salkinium/checkirona/pcb/stm32f4_adapter.sch

## EAGLE design pcb/stm32f4_adapter.sch (2015-05-14)

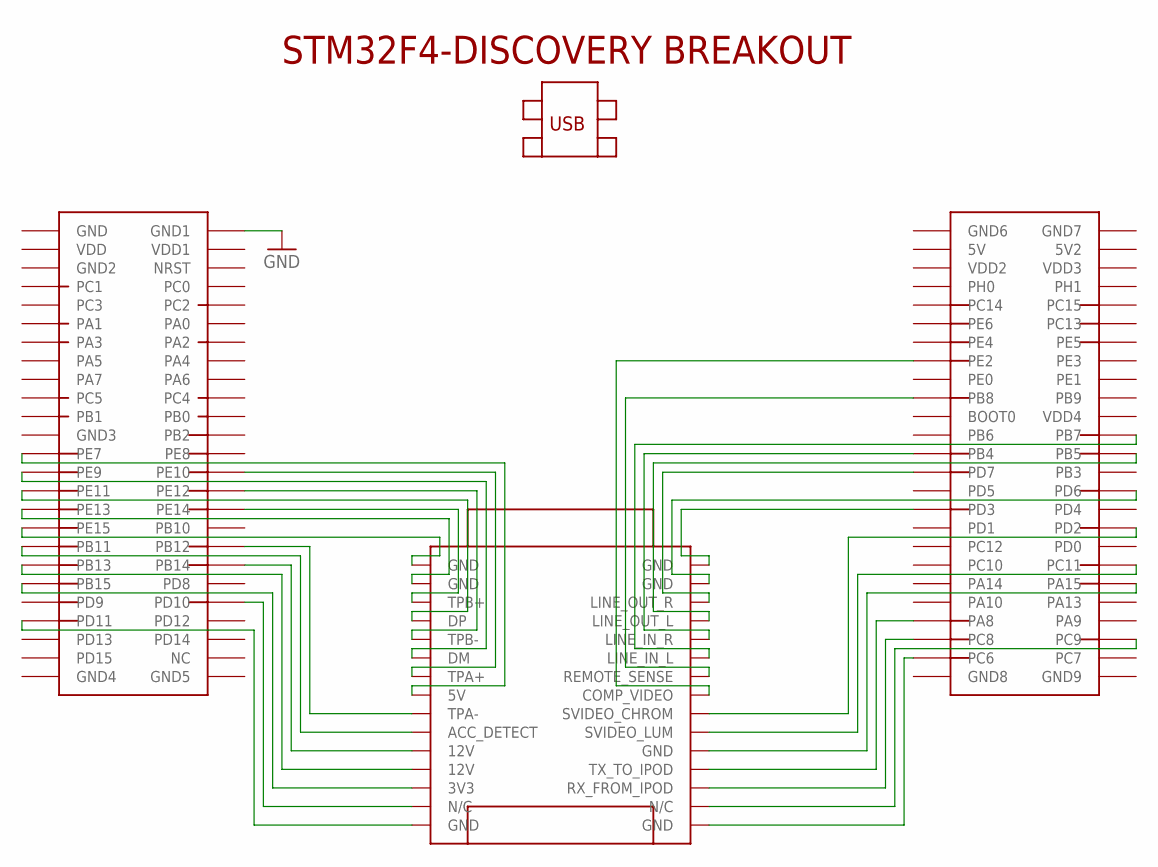
[picture p3: schematic stm32f4_adapter.sch]

Parts:
U$1: STM32F4-DISCOVERY
U$2: IPOD-CONNECTOR

Connections:
GND: U$1.P$2 (GND1)
unnamed: U$1.P$43 (PD11), U$2.P$16 (GND)
unnamed: U$1.P$42 (PD10), U$2.P$17 (N/C)
unnamed: U$1.P$39 (PB15), U$2.P$18 (3V3)
unnamed: U$1.P$38 (PB14), U$2.P$20 (12V)
unnamed: U$1.P$37 (PB13), U$2.P$19 (12V)
unnamed: U$1.P$36 (PB12), U$2.P$22 (TPA-)
unnamed: U$1.P$35 (PB11), U$2.P$21 (ACC_DETECT)
unnamed: U$1.P$33 (PE15), U$2.P$30 (GND)
unnamed: U$1.P$32 (PE14), U$2.P$28 (TPB+)
unnamed: U$1.P$31 (PE13), U$2.P$29 (GND)
unnamed: U$1.P$30 (PE12), U$2.P$26 (TPB-)
unnamed: U$1.P$29 (PE11), U$2.P$27 (DP)
unnamed: U$1.P$27 (PE9), U$2.P$25 (DM)
unnamed: U$1.P$28 (PE10), U$2.P$24 (TPA+)
unnamed: U$1.P$25 (PE7), U$2.P$23 (5V)
unnamed: U$1.P$97 (PC6), U$2.P$15 (GND)
unnamed: U$1.P$96 (PC9), U$2.P$14 (N/C)
unnamed: U$1.P$95 (PC8), U$2.P$13 (RX_FROM_IPOD)
unnamed: U$1.P$93 (PA8), U$2.P$12 (TX_TO_IPOD)
unnamed: U$1.P$90 (PA15), U$2.P$11 (GND)
unnamed: U$1.P$88 (PC11), U$2.P$10 (SVIDEO_LUM)
unnamed: U$1.P$84 (PD2), U$2.P$9 (SVIDEO_CHROM)
unnamed: U$1.P$65 (PE2), U$2.P$8 (COMP_VIDEO)
unnamed: U$1.P$80 (PD6), U$2.P$2 (GND)
unnamed: U$1.P$77 (PD7), U$2.P$3 (LINE_OUT_R)
unnamed: U$1.P$76 (PB5), U$2.P$4 (LINE_OUT_L)
unnamed: U$1.P$75 (PB4), U$2.P$5 (LINE_IN_R)
unnamed: U$1.P$74 (PB7), U$2.P$6 (LINE_IN_L)
unnamed: U$1.P$69 (PB8), U$2.P$7 (REMOTE_SENSE)
unnamed: U$1.P$81 (PD3), U$2.P$1 (GND)
